Sai25622/jetson-flir-enclosure-system/Images/lock nut.png

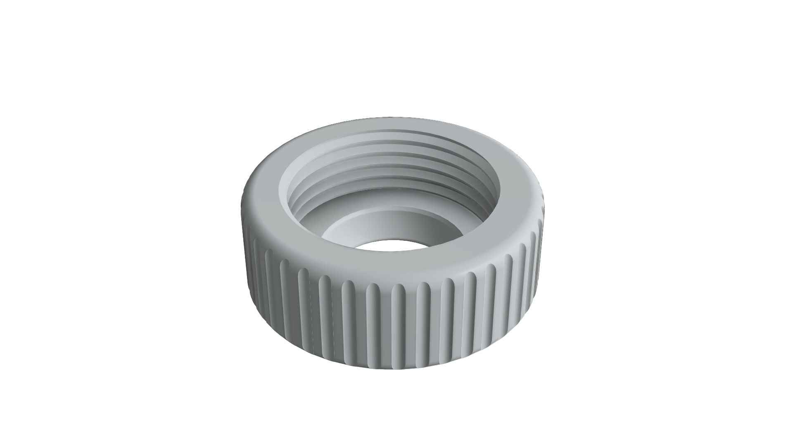
Images/lock nut.png
