Sai25622/jetson-flir-enclosure-system/Images/mount.png

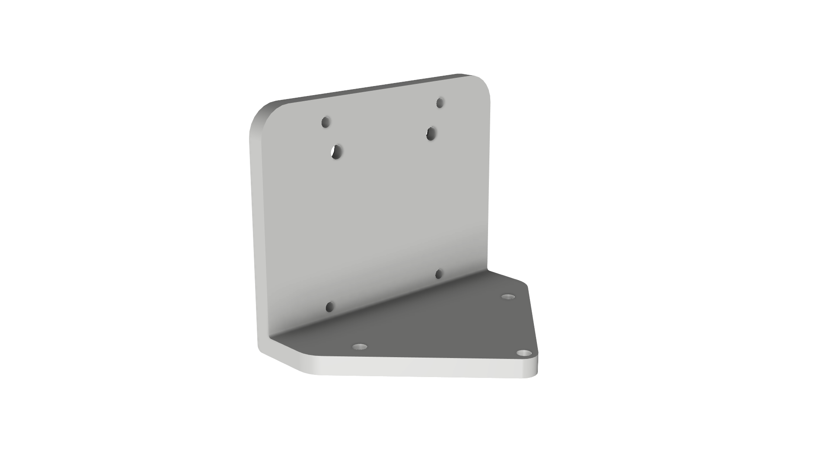
Images/mount.png
