Sai25622/jetson-flir-enclosure-system/Images/socket arm.png

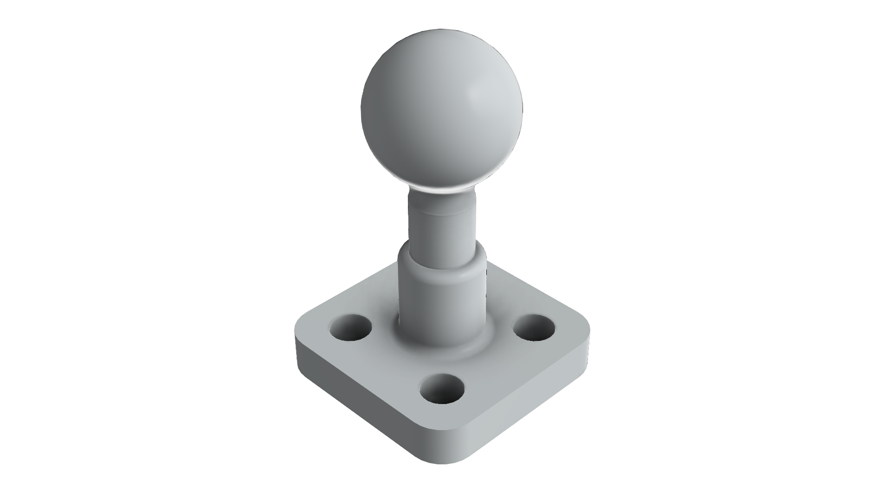
Images/socket arm.png
